funkyfourier/dogtreatbox/release/v1/pics/Box02.jpg

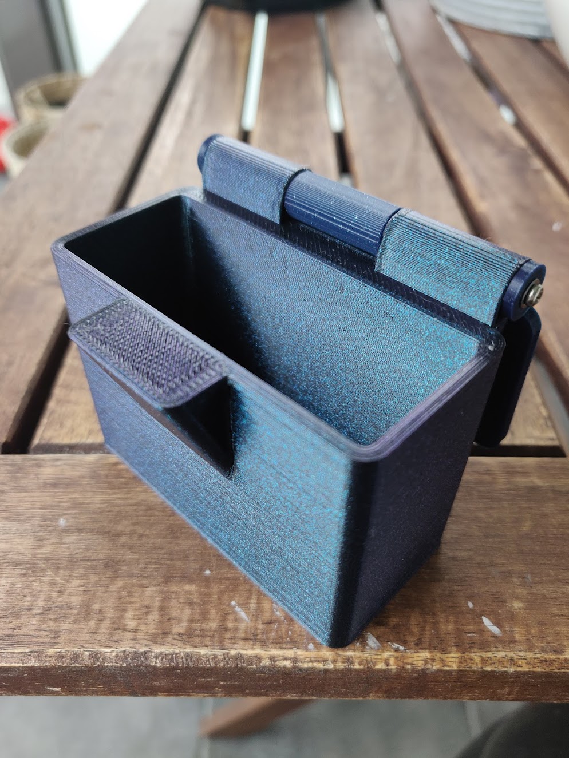
release/v1/pics/Box02.jpg
