funkyfourier/dogtreatbox/release/v1/pics/Box03.jpg

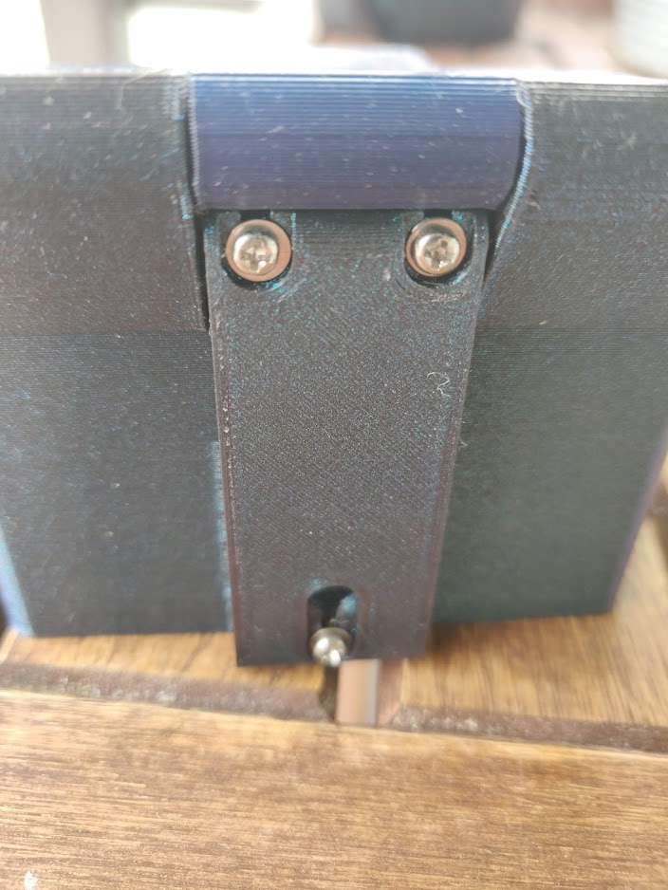
release/v1/pics/Box03.jpg
